dchwebb/MidiMonger/pictures/midimonger2_back2.jpg

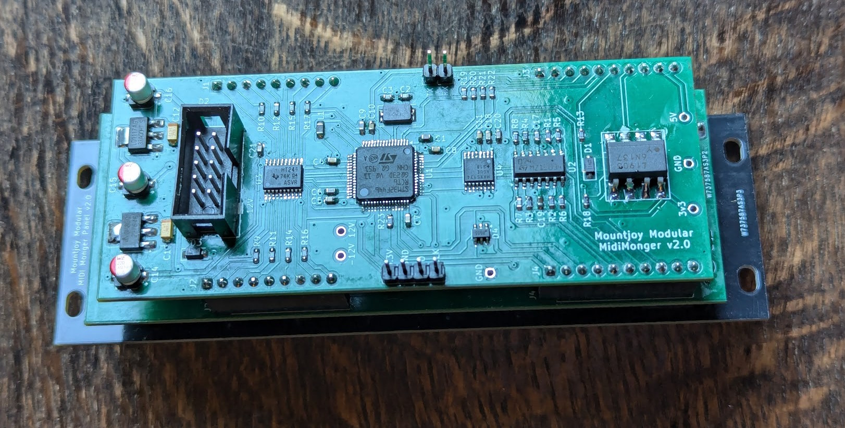
pictures/midimonger2_back2.jpg
