dchwebb/MidiMonger/pictures/midimonger2_back.jpg

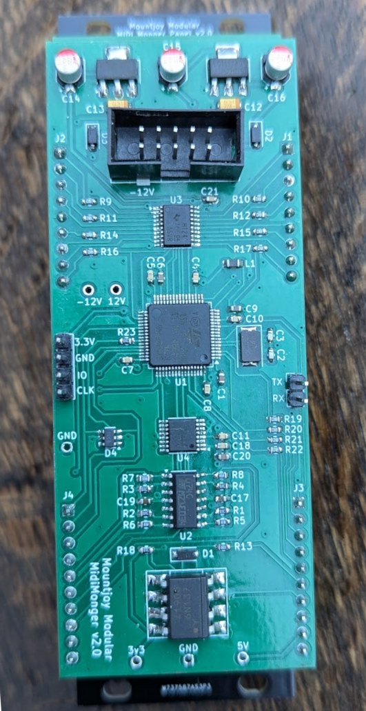
pictures/midimonger2_back.jpg
