dchwebb/MidiMonger/pictures/MidiMonger.png

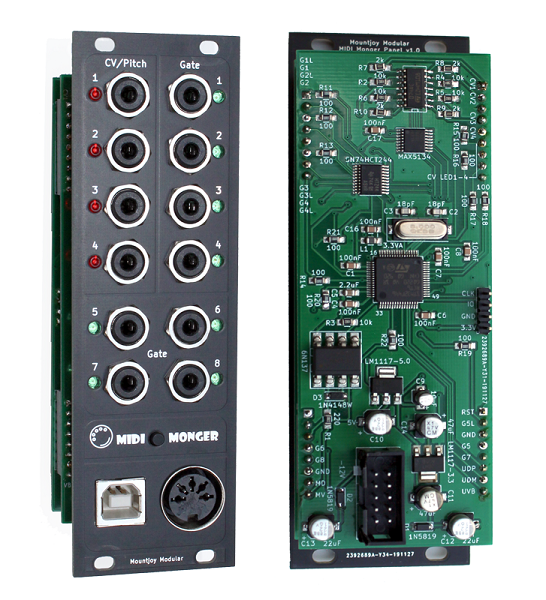
pictures/MidiMonger.png
