dchwebb/MidiMonger/pictures/panel.png

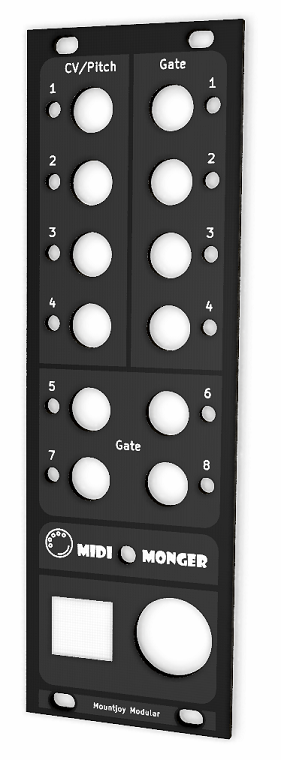
pictures/panel.png
