dchwebb/MidiMonger/MidiMonger2/src/USBHost/HidHostClass.cpp

#include "HidHostClass.h"
#include "USBHost.h"
#include "MidiControl.h"
#include <limits>

HidHostClass hidHostClass(&usbHost, HidHostClass::name, HidHostClass::classCode);

HostStatus HidHostClass::InterfaceInit()
{
	printf("HID Class Init\n");

	auto interfaceDesc = usbHost->SelectInterface(classCode, usbBootSubclass);
	if (interfaceDesc == nullptr) {
		printf("Cannot Find the interface for %s class\n", name);
		return HostStatus::Fail;
	}

	inPipe = 0;
	inEp = 0;
	outPipe = 0;
	outEp = 0;
	timer = 0;
	state = HidState::Init;
	epAddr = interfaceDesc->epDesc[0].bEndpointAddress;
	packetSize = interfaceDesc->epDesc[0].wMaxPacketSize;
	poll = std::min(interfaceDesc->epDesc[0].bInterval, hidMinPoll);

	uint8_t endpoints = std::min(interfaceDesc->bNumEndpoints, USBHost::maxNumEndpoints);

	// Decode endpoint IN and OUT address from interface descriptor
	for (uint8_t i = 0; i < endpoints; ++i) {
		if (interfaceDesc->epDesc[i].bEndpointAddress & 0x80) {
			inEp = interfaceDesc->epDesc[i].bEndpointAddress;
			inPipe = usbHost->AllocPipe(inEp);

			// Open pipe for IN endpoint
			usbHost->HostChannelInit(inPipe, inEp, usbHost->device.address, usbHost->device.speed, USBHost::Bulk, packetSize);
			usbHost->SetToggle(inPipe, 0);
		} else {
			outEp = interfaceDesc->epDesc[i].bEndpointAddress;
			outPipe  = usbHost->AllocPipe(outEp);

			// Open pipe for OUT endpoint
			usbHost->HostChannelInit(outPipe, outEp, usbHost->device.address, usbHost->device.speed, USBHost::Bulk, packetSize);
			usbHost->SetToggle(outPipe, 0);
		}
	}

	return HostStatus::OK;
}


void HidHostClass::InterfaceDeInit()
{
	printf("HID Class DeInit\n");

	if (inPipe != 0) {
		usbHost->HaltChannel(inPipe);
		usbHost->FreePipe(inPipe);
		inPipe = 0;					// Reset the pipe as Free
	}

	if (outPipe != 0) {
		usbHost->HaltChannel(outPipe);
		usbHost->FreePipe(outPipe);
		outPipe = 0;    			// Reset the pipe as Free
	}

	state = HidState::Init;
}


HostStatus HidHostClass::Process()
{
	// Manages state machine for Hid data transfers
	switch (state) {
	case HidState::Init:
		if (usbHost->timer & 1) {			// Sync with start of Even Frame
			printf("HID Class Process: Init\n");
			state = HidState::GetReportDesc;
		}
		break;

	case HidState::GetReportDesc:			// Get HID Report Descriptor
		if (GetReportDesc()) {
			hidDescriptor.ParseReportDesc();
			hidDescriptor.PrintReportDesc();
			state = HidState::GetData;
			printf("HID Report Descriptor Parsed\n");
		}
		break;

	case HidState::GetData:
		usbHost->StartTransfer(inPipe, USBHost::pidToken::Data, hidBuffer, packetSize);
		state = HidState::Poll;
		timer = usbHost->timer;
		poll = SysTickVal;
		break;

	case HidState::Poll:
		if (usbHost->GetURBState(inPipe) == USBHost::URBState::Done) {
			if (usbHost->GetTransferCount(inPipe) > 0) {
				HidEvent(hidBuffer, packetSize);
			}
			state = HidState::Wait;

		} else if (usbHost->GetURBState(inPipe) == USBHost::URBState::Stall) {
			if (usbHost->ClearFeature(epAddr) == HostStatus::OK) {		// Issue Clear Feature on interrupt IN endpoint
				state = HidState::Wait;									// Change state to issue next IN token
			}
		}
		break;

	case HidState::Wait:
		state = HidState::GetData;
//		if (SysTickVal > poll + 1) {			// Test to apply a delay between each poll
//			state = HidState::GetData;
//		}

	default:
		break;
	}

	return HostStatus::OK;
}


bool HidHostClass::GetReportDesc()
{
	HostStatus status = usbHost->ClassRequest(USBHost::requestRecipientInterface | USBHost::requestTypeStandard,
			USBHost::RequestGetDescriptor,
			USB_DESC_HID_REPORT,
			0,
			hidDescriptor.rawDesc,
			hidDescriptor.hidDescSize);

	if (status == HostStatus::OK) {		// Commands successfully sent and Response Received
		return true;
	}
	return false;
}


bool HidHostClass::GetReport(uint8_t reportType, uint8_t reportId)
{
	// reportType = 1; reportId = 0
	HostStatus status = usbHost->ClassRequest(USBHost::requestRecipientInterface | USBHost::RequestTypeClass,
			getReport,
			(reportType << 8) | reportId,
			0,
			hidBuffer,
			packetSize);

	if (status == HostStatus::OK) {		// Commands successfully sent and Response Received
		return true;
	}
	return false;
}


int32_t HidHostClass::ParseReport(uint8_t* buff, uint32_t offset, uint32_t size)
{
	if (offset + size <= 64) {				// useful for fiddly lengths such as 12 bit values
		uint64_t data = *(uint64_t*)buff;
		if (size == 12) {
			uint16_t u12 = (data >> offset) & 0xFFF;
			if (u12 & (1 << 11)) {			// if signed, bit 11 set
				u12 |= 0xFF << 12;			// sign extend
			}
			return (int16_t)u12;
		} else if (size == 8) {
			return (int8_t)((data >> offset) & 0xFF);
		} else if (size == 16) {
			return (int16_t)((data >> offset) & 0xFFFF);
		}
		return (data >> offset) & ((1 << size) - 1);
	} else if (size == 16) {
		return *(int16_t*)&buff[offset];
	} else if (size == 8) {
		return (int8_t)buff[offset >> 3];
	} else {
		return 0;
	}
}

void HidHostClass::HidEvent(uint8_t* buff, uint16_t len)
{
	// Moving mouse forwards = negative y
	int32_t mouse[hidDescriptor.ControlsCount] = {0};
	uint32_t buttons = 0;

	for (uint32_t i = 0; i < hidDescriptor.ControlsCount; ++i) {
		if (hidDescriptor.controls[i].Offset + hidDescriptor.controls[i].Size) {
			mouse[i] = ParseReport(buff, hidDescriptor.controls[i].Offset, hidDescriptor.controls[i].Size);
			hidValues.controls[i] = std::clamp(hidValues.controls[i] + (mouse[i] * cfg.mouseScale[i]), 0L, (int32_t)std::numeric_limits<uint16_t>::max());

			if (mouse[i] && i < 4) {
				for (uint32_t cv = 0; cv < 4; ++cv) {								// Check if mouse control is linked to each CV output
					if ((cfg.cvSource[cv] == mouseX && i == HidDescriptor::X) ||
						(cfg.cvSource[cv] == mouseY && i == HidDescriptor::Y) ||
						(cfg.cvSource[cv] == mouseWheel && i == HidDescriptor::Wheel)) {
						midiControl.SendCV(hidValues.controls[i], cv, 100);
					}
				}

			}
		}
	}

	if (hidDescriptor.buttonOffset + hidDescriptor.buttonCount) {
		buttons = buff[hidDescriptor.buttonOffset >> 3];
		if (buttons != hidValues.buttons) {
			for (uint8_t i = 0; i < 8; ++i) {
				uint8_t buttonChanged = 2;		// State unchanged

				if (buttons & (1 << i) && (hidValues.buttons & (1 << i)) == 0) {
					buttonChanged = 1;				// Button pressed

				} else if ((buttons & (1 << i)) == 0 && hidValues.buttons & (1 << i)) {
					buttonChanged = 0;				// Button released
				}
				if (buttonChanged < 2) {
					for (uint8_t g = 0; g < 8; ++g) {
						if (cfg.gateSource[g] == (GateSource)(i + 1)) {
							midiControl.SendGate(g, buttonChanged);
						}
					}
				}


			}
			hidValues.buttons = buttons;
		}
	}
	//printf("Hid X: %ld Y: %ld; Wheel: %ld; Buttons: %lu\r\n", mouse[HidDescriptor::X], mouse[HidDescriptor::Y], mouse[HidDescriptor::Wheel], buttons);

}


void HidHostClass::SetConfig()
{

}
