dchwebb/MidiMonger/MidiMonger2/src/USBHost/MidiHostClass.cpp

#include "MidiHostClass.h"
#include "USBHost.h"
#include "MidiControl.h"

MidiHostClass midiHostClass(&usbHost, MidiHostClass::name, MidiHostClass::classCode);

HostStatus MidiHostClass::InterfaceInit()
{
	printf("MIDI Class Init\n");

	// Attempt to find the Midi interface to locate the correct endpoints and other settings
	auto interfaceDesc = usbHost->SelectInterface(classCode, usbMidiStreamingSubclass);
	if (interfaceDesc == nullptr) {
		printf("Cannot Find the interface for %s class\n", name);
		return HostStatus::Fail;
	}

	inPipe = 0;
	inEp = 0;
	outPipe = 0;
	outEp = 0;
	timer = 0;
	state = MidiState::Init;
	epAddr = interfaceDesc->epDesc[0].bEndpointAddress;
	packetSize = interfaceDesc->epDesc[0].wMaxPacketSize;
	poll = std::min(interfaceDesc->epDesc[0].bInterval, midiMinPoll);

	uint8_t endpoints = std::min(interfaceDesc->bNumEndpoints, USBHost::maxNumEndpoints);

	// Decode endpoint IN and OUT address from interface descriptor
	for (uint8_t i = 0; i < endpoints; ++i) {
		if (interfaceDesc->epDesc[i].bEndpointAddress & USBHost::DeviceToHost) {
			inEp = interfaceDesc->epDesc[i].bEndpointAddress;
			inPipe = usbHost->AllocPipe(inEp);

			// Open pipe for IN endpoint
			usbHost->HostChannelInit(inPipe, inEp, usbHost->device.address, usbHost->device.speed, USBHost::Bulk, packetSize);
			usbHost->SetToggle(inPipe, 0);
		} else {
			outEp = interfaceDesc->epDesc[i].bEndpointAddress;
			outPipe = usbHost->AllocPipe(outEp);

			// Open pipe for OUT endpoint
			usbHost->HostChannelInit(outPipe, outEp, usbHost->device.address, usbHost->device.speed, USBHost::Bulk, packetSize);
			usbHost->SetToggle(outPipe, 0);
		}
	}

	return HostStatus::OK;
}


void MidiHostClass::InterfaceDeInit()
{
	printf("MIDI Class DeInit\n");

	if (inPipe != 0) {
		usbHost->HaltChannel(inPipe);
		usbHost->FreePipe(inPipe);
		inPipe = 0;					// Reset the pipe as Free
	}

	if (outPipe != 0) {
		usbHost->HaltChannel(outPipe);
		usbHost->FreePipe(outPipe);
		outPipe = 0;    			// Reset the pipe as Free
	}

	state = MidiState::Init;
}


HostStatus MidiHostClass::Process()
{
	// Manages state machine for Midi data transfers
	switch (state) {
	case MidiState::Init:
		if (usbHost->timer & 1) {		// Sync with start of Even Frame
			midiControl.LightShow(MidiControl::LightShowType::connection);
			printf("MIDI Class Process: Init\n");
			state = MidiState::GetData;
		}
		break;

	case MidiState::GetData:
		usbHost->StartTransfer(inPipe, USBHost::pidToken::Data, midiBuffer, packetSize);
		state = MidiState::Poll;
		timer = usbHost->timer;
		break;

	case MidiState::Poll:
		if (usbHost->GetURBState(inPipe) == USBHost::URBState::Done) {
			const uint32_t xferCount = usbHost->GetTransferCount(inPipe);
			if (xferCount > 0) {
				MidiEvent((uint32_t*)midiBuffer, xferCount);
			}
			state = MidiState::GetData;

		} else if (usbHost->GetURBState(inPipe) == USBHost::URBState::Stall) {
			if (usbHost->ClearFeature(epAddr) == HostStatus::OK) {		// Issue Clear Feature on interrupt IN endpoint
				state = MidiState::GetData;								// Change state to issue next IN token
			}
		}
		break;

	default:
		break;
	}

	return HostStatus::OK;
}


uint32_t debugMIDImultiEvents = 0;
uint32_t debugMIDIsplitEvents = 0;

void MidiHostClass::MidiEvent(uint32_t* buff, uint16_t len)
{
	uint32_t events = (len + 3) / 4;				// len is in bytes

	if (len != 4) {
		++debugMIDImultiEvents;
	}
	if (events != len / 4) {
		++debugMIDIsplitEvents;
	}


	for (uint32_t i = 0; i < events; ++i) {
		midiControl.MidiEvent(*buff);
		++buff;
	}


//	static uint32_t clkCnt = 0;
//
//	uint32_t midiData = *(uint32_t*)buff;
//	if (midiData == 0xF80F) {
//		if (clkCnt == 0) {
//			printf("Clock\r\n");
//		}
//		++clkCnt;
//	} else {
//		if (clkCnt > 0) {
//			printf("Clock: %ld\r\n", clkCnt);
//			clkCnt = 0;
//		}
//		printf("Midi: 0x%08lx\r\n", midiData);
//	}
}
