dchwebb/MidiMonger/bu/MidiMonger_446/src/initialisation.h

#pragma once

#include "stm32f4xx.h"
#include <algorithm>

extern volatile uint32_t SysTickVal;

void InitClocks(void);
void InitIO(void);
void InitSysTick();
void InitSampleAcquisition();
void InitCoverageTimer();
void InitDebounceTimer();
void InitEncoders();
void InitMidiUART();
void InitDAC();
